hackEns/2048NdS/pc_control/predefined_colors.py

# -*- coding: utf8 -*-

rose = {'r': 232, 'g': 30, 'b': 116}
black = {'r': 0, 'g': 0, 'b': 0}
white = {'r': 255, 'g': 255, 'b': 255}
red = {'r': 255, 'g': 0, 'b': 0}
green = {'r': 0, 'g': 255, 'b': 0}
blue = {'r': 0, 'g': 0, 'b': 255}
orange = {'r': 203, 'g': 75, 'b': 22}
yellow = {'r': 181, 'g': 137, 'b': 0}
brown = {'r': 139, 'g': 69, 'b': 19}
purple = {'r': 98, 'g': 103, 'b': 186}
skyblue = {'r': 42, 'g': 161, 'b': 152}

# magenta   #d33682 211  54 130 = rose
# yellow    #b58900 181 137   0 = yellow
# orange    #cb4b16 203  75  22 = orange
# red       #dc322f 220  50  47 = red
# violet    #6c71c4 108 113 196 = purple
# blue      #268bd2  38 139 210 = blue
# cyan      #2aa198  42 161 152 = skyblue
# green     #859900 133 153   0 = green
